miketoos/interface_mesure/Partie_Hardware/Carte_electronique/Test_CIFAM/Cifam.h

#ifndef __Cifam_H__
#define __Cifam_H__


// Modes Classes
#define MODE_INJECTION 1
#define MODE_TEMPRETARD 2

// SAMD21
#define LED_DEBUG 15
#define IN1 18
#define IN2 19
#define IN3 22
#define IN4 23

// Pin DAC
#define DACCLEAR 10
#define DACDLDAC 11

// DAC
#define ADDRESS_DAC 0x48
#define OUT1 0x30
#define OUT2 0x31
#define OUT3 0x32
#define OUT4 0x33

#endif
