miketoos/interface_mesure/Partie_Hardware/Carte_electronique/Test_CIFAM/Mode.hpp

#ifndef __Mode_HPP__
#define __Mode_HPP__

class MODE
{
private:
    
public:
    MODE(); 
    MODE(int mode);
    ~MODE();

    virtual void Chrono1();
    virtual void Chrono2();
    virtual void Chrono3();
    virtual void Chrono4();
};




#endif
